jubeormk1/AnalogDiscovery_x20_powerMainsProbe/output/AnalogDiscovery_x20_powerMainsProbe.png

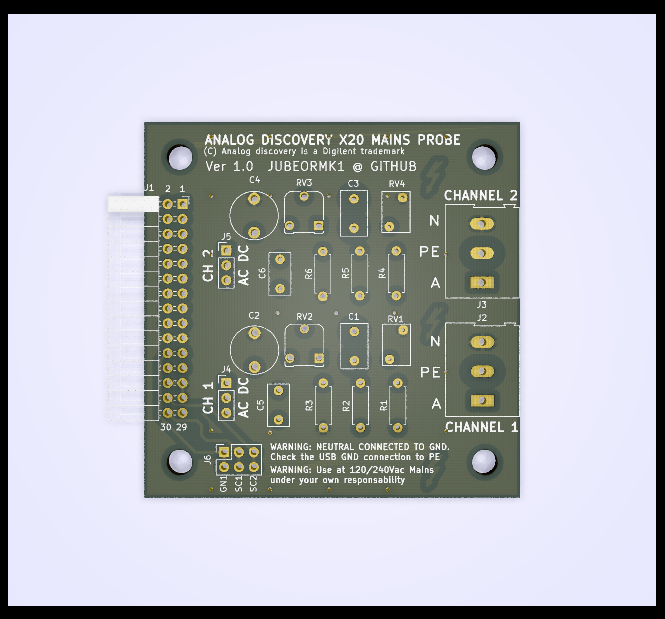
output/AnalogDiscovery_x20_powerMainsProbe.png
